SunnyCodes86/nightkite-multi/measurements/2026-05-28_061232_pattern_brightness_sweep/summary_per_segment.csv

segment_id | pattern_id | pattern_name | brightness | samples | duration_s | avg_voltage_v | avg_current_ma | median_current_ma | min_current_ma | max_current_ma | avg_power_w | max_power_w | consumed_mah | consumed_wh | status
seg_001_p01_b095 | 1 | rainbow | 95 | 52 | 5.187 | 4.0322 | 180.649 | 180.000 | 178.750 | 182.500 | 0.7284 | 0.7359 | 0.260938 | 0.001052 | ok
seg_002_p01_b127 | 1 | rainbow | 127 | 51 | 5.086 | 4.0191 | 215.392 | 215.000 | 213.750 | 218.750 | 0.8657 | 0.8791 | 0.305139 | 0.001226 | ok
seg_003_p01_b159 | 1 | rainbow | 159 | 53 | 5.229 | 4.0057 | 247.995 | 247.500 | 246.250 | 251.250 | 0.9934 | 1.0066 | 0.365104 | 0.001462 | ok
seg_004_p01_b191 | 1 | rainbow | 191 | 52 | 5.113 | 3.9917 | 280.096 | 280.000 | 278.750 | 283.750 | 1.1181 | 1.1325 | 0.404583 | 0.001615 | ok
seg_005_p01_b223 | 1 | rainbow | 223 | 51 | 5.115 | 3.9777 | 310.564 | 310.000 | 308.750 | 313.750 | 1.2353 | 1.2479 | 0.439965 | 0.001750 | ok
seg_006_p01_b255 | 1 | rainbow | 255 | 51 | 5.070 | 3.9636 | 340.539 | 340.000 | 338.750 | 345.000 | 1.3498 | 1.3675 | 0.482431 | 0.001912 | ok
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
