SunnyCodes86/nightkite-multi/measurements/2026-05-28_061232_pattern_brightness_sweep/summary_pivot.csv

average_current_ma
pattern_id | pattern_name | b95 | b127 | b159 | b191 | b223 | b255
1 | rainbow | 180.649 | 215.392 | 247.995 | 280.096 | 310.564 | 340.539
2 | full_color | 159.080 | 187.981 | 215.956 | 243.750 | 269.615 | 295.385
3 | motion_brightness | 98.652 | 98.798 | 98.822 | 99.014 | 98.799 | 99.038
4 | runner_fixed | 81.010 | 84.552 | 88.186 | 91.995 | 95.542 | 99.327
5 | runner_reactive | 89.062 | 95.433 | 102.163 | 108.625 | 114.856 | 121.202
6 | runner_dual | 91.538 | 98.848 | 105.986 | 113.255 | 120.409 | 127.099
7 | heartbeat | 79.447 | 82.404 | 85.259 | 88.702 | 91.683 | 95.000
8 | ping_pong | 78.750 | 81.394 | 84.175 | 87.005 | 89.712 | 92.716
9 | comet_swarm | 89.811 | 96.745 | 103.029 | 109.279 | 116.038 | 122.877
10 | breath_storm | 87.594 | 94.033 | 99.741 | 105.553 | 111.910 | 118.066
11 | jerk_wave | 70.361 | 73.365 | 70.307 | 70.425 | 70.385 | 70.330
12 | yaw_spinner | 77.429 | 80.189 | 84.207 | 87.043 | 91.321 | 90.849
13 | yaw_spinner_circle | 78.726 | 80.601 | 84.712 | 88.962 | 89.245 | 89.663
14 | runner_dual_inverted | 90.165 | 98.491 | 105.385 | 112.428 | 119.567 | 126.667
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
